ilove737/XS40/soft/Sample_Code/GPIO/Code/GPIO.C

#include "N76E003.h"
#include "SFR_Macro.h"
#include "Function_define.h"
#include "Common.h"
#include "Delay.h"
#include <string.h>
#include "keyMap.h"

// #define row1 P00
// #define row2 P01
// #define row3 P02
// #define row4 P03
// #define row5 P04

// #define col1 P10
// #define col2 P11
// #define col3 P12
// #define col4 P13
// #define col5 P14
// #define col6 P15
// #define col7 P16
// #define col8 P17

UINT8 xdata i, j;
UINT8 xdata beforeAllKey[5]; // 40个位，保存上一次所有40个建的状态
UINT8 xdata allKey[5];		 // 40个位，保存当前所有40个建的状态

UINT8 xdata kCode;
UINT8 xdata HIDFrames[8];
UINT8 xdata HIDFramesPointer = 2; // 从帧的第三个字节开始添加普通按键的KeyCode

UINT8 xdata Fn0_Status = 0;
UINT8 xdata Fn1_Status = 0;

UINT8 xdata tttt = 0;
UINT16 xdata TH1_INIT = 333;

void makeHIDFrames(void)
{
	Fn0_Status = 0;
	HIDFramesPointer = 2;
	for (i = 0; i < 8; i++)
	{
		HIDFrames[i] = 0;
	}
	if (allKey[0] == 0 && allKey[1] == 0 && allKey[2] == 0 && allKey[3] == 0 && allKey[4] == 0)
	{ // 所有按键都是松开的状态
		for (i = 0; i < 8; i++)
		{
			Send_Data_To_UART0(0x00);
		}
	}
	else
	{ // 有按键按下的状态
		for (i = 0; i < 5; i++)
		{
			if (allKey[i] != 0)
			{
				for (j = 0; j < 8; j++)
				{
					if (allKey[i] >> j & 1)
					{
						if (keyMap[i * 8 + j] == KEY_Fn0)
						{
							Fn0_Status = 1;
						}
						if (keyMap[i * 8 + j] == KEY_Fn1)
						{
							Fn1_Status = 1;
						}
					}
				}
			}
		}

		for (i = 0; i < 5; i++)
		{
			if (allKey[i] != 0)
			{
				for (j = 0; j < 8; j++)
				{
					if (allKey[i] >> j & 1)
					{
						if (Fn0_Status == 1)
						{
							kCode = Fn0_keyMap[i * 8 + j];
						}
						else
						{
							kCode = keyMap[i * 8 + j];
						}
						// if (kCode == KEY_LCTRL | kCode == KEY_LSHIFT | kCode == KEY_LALT | kCode == KEY_LGUI | kCode == KEY_RCTRL | kCode == KEY_RSHIFT | kCode == KEY_RALT | kCode == KEY_RGUI)
						if (kCode >= 0xE0) // Control
						{
							HIDFrames[0] += 0X01 << (kCode & 0X0F);
						}
						else if (kCode >= 0xC0) // 处理shift组合键
						{
							HIDFrames[0] += 0x02;
							HIDFrames[HIDFramesPointer] = kCode - 0xa2;
							HIDFramesPointer++;
						}
						else
						{
							HIDFrames[HIDFramesPointer] = kCode;
							HIDFramesPointer++;
						}
					}
				}
			}
		}
		for (i = 0; i < 8; i++)
		{
			Send_Data_To_UART0(HIDFrames[i]);
		}
	}
}

// 系统时钟      16000 / 16000000 = 0.001s
// 系统时钟1/12  1333  / 1333333  = 0.001s
void Timer1_ISR(void) interrupt 3 //interrupt address is 0x001B
{
	TH1 = (65536 - TH1_INIT) / 256;
	TL1 = (65536 - TH1_INIT) % 256;

	// row1到row5依次拉低
	P0 = 0xFF;
	if (tttt == 5) //所有键扫描完成
	{
		tttt = 0;
		if (memcmp(beforeAllKey, allKey, 5) != 0)
		{
			memcpy(beforeAllKey, allKey, 5);

			makeHIDFrames();
			// Send_Data_To_UART0(allKey[i]);
		}
	}
	else
	{
		if (tttt == 0)
			P00 = 0;
		if (tttt == 1)
			P01 = 0;
		if (tttt == 2)
			P02 = 0;
		if (tttt == 3)
			P03 = 0;
		if (tttt == 4)
			P04 = 0;

		allKey[tttt] = ~P1;

		tttt++;
	}
}

void main(void)
{
	///////////////////////////////////WDT///////////////////////////////////////
	TA = 0xAA;
	TA = 0x55;
	WDCON = 0x07; //Setting WDT prescale
	set_WDTR;	  //WDT run
	set_WDCLR;	  //Clear WDT timer
	set_EWDT;
	EA = 1;
	//set_WIDPD;
	/////////////////////////////////////////////////////////////////////////////

	Set_All_GPIO_Quasi_Mode;

	P00_PushPull_Mode;
	P01_PushPull_Mode;
	P02_PushPull_Mode;
	P03_PushPull_Mode;
	P04_PushPull_Mode;

	TIMER1_MODE1_ENABLE;
	// set_T1M;
	TH1 = (65536 - TH1_INIT) / 256;
	TL1 = (65536 - TH1_INIT) % 256;
	set_ET1; //enable Timer1 interrupt
	set_EA;	 //enable interrupts
	set_TR1; //Timer1 run

	InitialUART0_Timer3(115200);
	// Enable_ADC_AIN1; // Enable AIN0 as ADC input, Find in "Function_define.h" - "ADC INIT"
	// Enable_ADC_AIN7;

	while (1)
	{
		set_WDCLR; // 喂狗
	}
}
